andres-garcia-alves/electronics-digital-thermometer/Resources/01-squematic-diagram-03.jpg

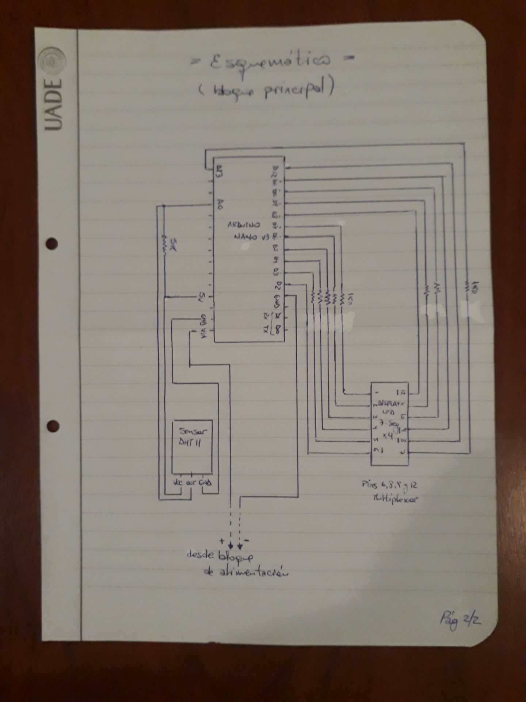
Resources/01-squematic-diagram-03.jpg
