andres-garcia-alves/electronics-digital-thermometer/Resources/02-pcb-layout-02.jpg

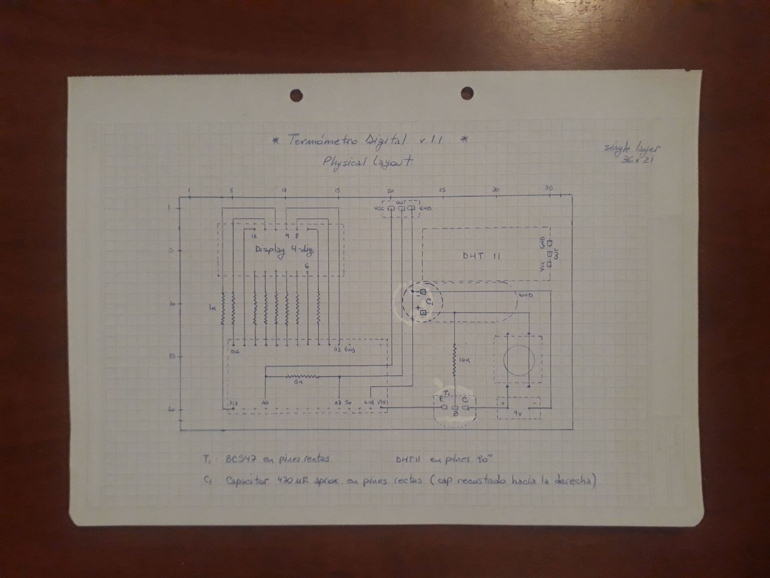
Resources/02-pcb-layout-02.jpg
