andres-garcia-alves/electronics-digital-thermometer/Resources/06-box-shaping-04.jpg

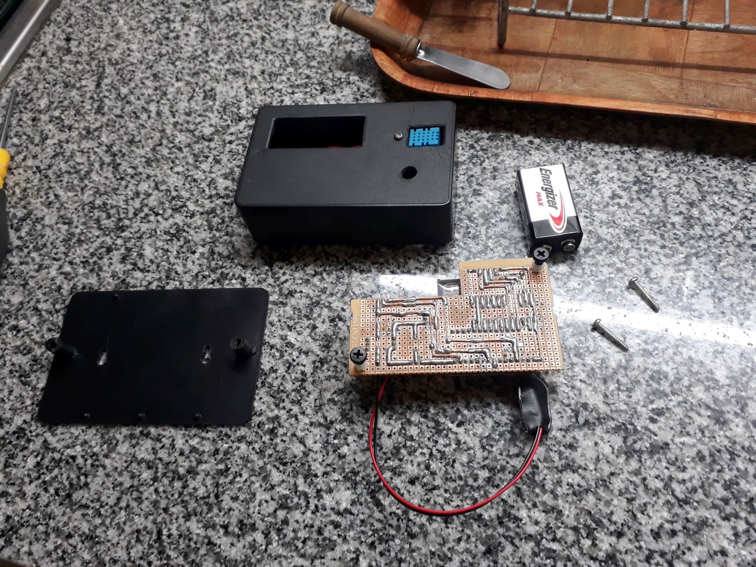
Resources/06-box-shaping-04.jpg
